CWempe/SuperLEDstrip/src/nextion_callback_functions.h

// Nextion components functions
// global
// page 1
void titlePopCallback(void *ptr) { }
void versionPopCallback(void *ptr) { }
void tempPopCallback(void *ptr) { }
void humidPopCallback(void *ptr) { }
void p01PopCallback(void *ptr) { }
void p01titlePopCallback(void *ptr) { }
void p01versionPopCallback(void *ptr) { }
void p01settingsPopCallback(void *ptr) { setTextAll(); }
void p01powerPopCallback(void *ptr) { toggleBrightness(); }
void p01t01PopCallback(void *ptr) { updateTab(); }
void p01t02PopCallback(void *ptr) { updateTab(); }
void p01t03PopCallback(void *ptr) { updateTab(); }
void p01t04PopCallback(void *ptr) { updateTab(); }
void p01t05PopCallback(void *ptr) { updateTab(); }
void p01t06PopCallback(void *ptr) { updateTab(); }
void p01t07PopCallback(void *ptr) { updateTab(); }
void p01c01PopCallback(void *ptr) { setScene(101); }
void p01c02PopCallback(void *ptr) { setScene(102); }
void p01c03PopCallback(void *ptr) { setScene(103); }
void p01c04PopCallback(void *ptr) { setScene(104); }
void p01c05PopCallback(void *ptr) { setScene(105); }
void p01c06PopCallback(void *ptr) { setScene(106); }
void p01c07PopCallback(void *ptr) { setScene(107); }
void p01c08PopCallback(void *ptr) { setScene(108); }
void p01c09PopCallback(void *ptr) { setScene(109); }
// page 2
void p02PopCallback(void *ptr) { }
void p02titlePopCallback(void *ptr) { }
void p02versionPopCallback(void *ptr) { }
void p02settingsPopCallback(void *ptr) { setTextAll(); }
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
void p06t04PopCallback(void *ptr) { updateTab(); }
void p06t05PopCallback(void *ptr) { updateTab(); }
void p06t06PopCallback(void *ptr) { updateTab(); }
void p06t07PopCallback(void *ptr) { updateTab(); }
void p06c01PopCallback(void *ptr) { setScene(601); }
void p06c02PopCallback(void *ptr) { setScene(602); }
void p06c03PopCallback(void *ptr) { setScene(603); }
void p06c04PopCallback(void *ptr) { }
void p06c05PopCallback(void *ptr) { }
void p06c06PopCallback(void *ptr) { }
void p06c07PopCallback(void *ptr) { }
void p06c08PopCallback(void *ptr) { }
// page 7
void p07PopCallback(void *ptr) { }
void p07titlePopCallback(void *ptr) { }
void p07versionPopCallback(void *ptr) { }
void p07settingsPopCallback(void *ptr) { setTextAll(); }
void p07powerPopCallback(void *ptr) { toggleBrightness(); }
void p07t01PopCallback(void *ptr) { updateTab(); }
void p07t02PopCallback(void *ptr) { updateTab(); }
void p07t03PopCallback(void *ptr) { updateTab(); }
void p07t04PopCallback(void *ptr) { updateTab(); }
void p07t05PopCallback(void *ptr) { updateTab(); }
void p07t06PopCallback(void *ptr) { updateTab(); }
void p07t07PopCallback(void *ptr) { updateTab(); }
void p07c01PopCallback(void *ptr) { setScene(110); }
void p07c02PopCallback(void *ptr) { setScene(112); }
void p07c03PopCallback(void *ptr) { setScene(111); }
void p07c04PopCallback(void *ptr) { }
void p07c05PopCallback(void *ptr) { setPalette(5); }
void p07c06PopCallback(void *ptr) { setPalette(3); }
void p07c07PopCallback(void *ptr) { setPalette(4); }
void p07c08PopCallback(void *ptr) { setPalette(100); }
void p07c09PopCallback(void *ptr) { setPalette(7); }
void p07c10PopCallback(void *ptr) { setPalette(102); }
void p07c11PopCallback(void *ptr) { }
void p07c12PopCallback(void *ptr) { }
void p07c13PopCallback(void *ptr) { }
void p07c14PopCallback(void *ptr) { }
void p07c15PopCallback(void *ptr) { }
void p07c16PopCallback(void *ptr) { }
// page 8
void p08PopCallback(void *ptr) { }
void p08titlePopCallback(void *ptr) { }
void p08versionPopCallback(void *ptr) { }
void p08settingsPopCallback(void *ptr) { setTextAll(); }
void p08powerPopCallback(void *ptr) { toggleBrightness(); }
void p08t01PopCallback(void *ptr) { updateTab(); }
void p08t02PopCallback(void *ptr) { updateTab(); }
void p08t03PopCallback(void *ptr) { updateTab(); }
void p08t04PopCallback(void *ptr) { updateTab(); }
void p08t05PopCallback(void *ptr) { updateTab(); }
void p08t06PopCallback(void *ptr) { updateTab(); }
void p08t07PopCallback(void *ptr) { updateTab(); }
void p08c01PopCallback(void *ptr) { setBrightness(DEFAULT_BRIGHTNESS); }
void p08c02PopCallback(void *ptr) { setBrightness(100); }
void p08c03PopCallback(void *ptr) { setBrightness(75); }
void p08c04PopCallback(void *ptr) { setBrightness(25); }
void p08c05PopCallback(void *ptr) { setTextTemp(); }
void p08c06PopCallback(void *ptr) { setTextHumid(); }
void p08c07PopCallback(void *ptr) { changeRotationSpeed(true); }
void p08c08PopCallback(void *ptr) { changeRotationSpeed(false); }
void p08temp02PopCallback(void *ptr) { }
void p08humid02PopCallback(void *ptr) { }
void p08speed01PopCallback(void *ptr) { changeRotationSpeed(true); }
// page 9
void p09PopCallback(void *ptr) { }
void p09titlePopCallback(void *ptr) { }
void p09versionPopCallback(void *ptr) { }
void p09settingsPopCallback(void *ptr) { setTextAll(); }
void p09powerPopCallback(void *ptr) { toggleBrightness(); }
void p09sliderRedPopCallback(void *ptr)    { getRed(); }
void p09redMPopCallback(void *ptr)         { getRed(); }
void p09redPPopCallback(void *ptr)         { getRed(); }
void p09sliderGreenPopCallback(void *ptr)  { getGreen(); }
void p09greenMPopCallback(void *ptr)       { getGreen(); }
void p09greenPPopCallback(void *ptr)       { getGreen(); }
void p09sliderBluePopCallback(void *ptr)   { getBlue(); }
void p09blueMPopCallback(void *ptr)        { getBlue(); }
void p09bluePPopCallback(void *ptr)        { getBlue(); }
void p09save1PopCallback(void *ptr)        { saveCustomColorPreset (1); }
void p09load1PopCallback(void *ptr)        { loadCustomColorPreset (1); }
void p09save2PopCallback(void *ptr)        { saveCustomColorPreset (2);  }
void p09load2PopCallback(void *ptr)        { loadCustomColorPreset (2);  }
