CWempe/SuperLEDstrip/src/nextion_declaration.h

// Nextion components deklaration
// global
// page 1


char sRotationSpeed[2] = "";

NexText   title       = NexText(  0, 19, "title");
NexText   version     = NexText(  0, 24, "version");
NexText   temp        = NexText(  0, 20, "temp");
NexText   humid       = NexText(  0, 21, "humid");

NexPage   p01         = NexPage(  0,  0, "p01");
NexText   p01title    = NexText(  0,  1, "p01title");
NexText   p01version  = NexText(  0, 25, "p01version");
NexButton p01settings = NexButton(0,  9, "p01settings");
NexButton p01power    = NexButton(0, 18, "p01power");
NexButton p01t01      = NexButton(0,  2, "p01t01");
NexButton p01t02      = NexButton(0,  3, "p01t02");
NexButton p01t03      = NexButton(0,  4, "p01t03");
NexButton p01t04      = NexButton(0,  5, "p01t04");
NexButton p01t05      = NexButton(0,  6, "p01t05");
NexButton p01t06      = NexButton(0,  7, "p01t06");
NexButton p01t07      = NexButton(0,  8, "p01t07");
NexButton p01c01      = NexButton(0, 10, "p01c01");
NexButton p01c02      = NexButton(0, 11, "p01c02");
NexButton p01c03      = NexButton(0, 12, "p01c03");
NexButton p01c04      = NexButton(0, 13, "p01c04");
NexButton p01c05      = NexButton(0, 14, "p01c05");
NexButton p01c06      = NexButton(0, 15, "p01c06");
NexButton p01c07      = NexButton(0, 16, "p01c07");
NexButton p01c08      = NexButton(0, 17, "p01c08");
NexButton p01c09      = NexButton(0, 23, "p01c09");
// page 2
NexPage   p02         = NexPage(  1,  0, "p02");
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
NexButton p08t04      = NexButton(7,  5, "p08t04");
NexButton p08t05      = NexButton(7,  6, "p08t05");
NexButton p08t06      = NexButton(7,  7, "p08t06");
NexButton p08t07      = NexButton(7,  8, "p08t07");
NexButton p08c01      = NexButton(7, 10, "p08c01");
NexButton p08c02      = NexButton(7, 11, "p08c02");
NexButton p08c03      = NexButton(7, 12, "p08c03");
NexButton p08c04      = NexButton(7, 13, "p08c04");
NexButton p08c05      = NexButton(7, 14, "p08c05");
NexButton p08c06      = NexButton(7, 15, "p08c06");
NexButton p08c07      = NexButton(7, 16, "p08c07");
NexButton p08c08      = NexButton(7, 17, "p08c08");
NexText   p08temp02   = NexText(  7, 19, "p08temp02");
NexText   p08humid02  = NexText(  7, 20, "p08humid02");
NexText   p08speed01  = NexText(  7, 29, "p08speed01");

// page 9
NexPage   p09            = NexPage(  8,  0, "p09");
NexText   p09title       = NexText(  8,  1, "p09title");
NexText   p09version     = NexText(  8, 31, "p09version");
NexButton p09settings    = NexButton(8, 10, "p09settings");
NexButton p09power       = NexButton(8, 12, "p09power");
NexSlider p09sliderRed   = NexSlider(8, 14, "p09sliderRed");
NexSlider p09sliderGreen = NexSlider(8, 15, "p09sliderGreen");
NexSlider p09sliderBlue  = NexSlider(8, 26, "p09sliderBlue");
NexButton p09redM        = NexButton(8, 11, "p09redM");
NexButton p09redP        = NexButton(8, 19, "p09redP");
NexButton p09greenM      = NexButton(8, 21, "p09greenM");
NexButton p09greenP      = NexButton(8, 22, "p09greenP");
NexButton p09blueM       = NexButton(8, 24, "p09blueM");
NexButton p09blueP       = NexButton(8, 25, "p09blueP");
NexText   p09red         = NexText(  8, 13, "p09red");
NexText   p09green       = NexText(  8, 20, "p09green");
NexText   p09blue        = NexText(  8, 23, "p09blue");
NexButton p09save1       = NexButton(8, 27, "p09save1");
NexButton p09load1       = NexButton(8, 29, "p09load1");
NexButton p09save2       = NexButton(8, 28, "p09save2");
NexButton p09load2       = NexButton(8, 30, "p09load2");
