CWempe/SuperLEDstrip/src/nextion_initialization.h

// Nextion components inizialization
// global
void NextionSetup()
{
    nexInit();
    // page 1
    p01.attachPop(p01PopCallback);
    title.attachPop(titlePopCallback);
    version.attachPop(versionPopCallback);
    p01title.attachPop(p01titlePopCallback);
    p01version.attachPop(p01versionPopCallback);
    p01settings.attachPop(p01settingsPopCallback);
    p01power.attachPop(p01powerPopCallback);
    p01t01.attachPop(p01t01PopCallback);
    p01t02.attachPop(p01t02PopCallback);
    p01t03.attachPop(p01t03PopCallback);
    p01t04.attachPop(p01t04PopCallback);
    p01t05.attachPop(p01t05PopCallback);
    p01t06.attachPop(p01t06PopCallback);
    p01t07.attachPop(p01t07PopCallback);
    p01c01.attachPop(p01c01PopCallback);
    p01c02.attachPop(p01c02PopCallback);
    p01c03.attachPop(p01c03PopCallback);
    p01c04.attachPop(p01c04PopCallback);
    p01c05.attachPop(p01c05PopCallback);
    p01c06.attachPop(p01c06PopCallback);
    p01c07.attachPop(p01c07PopCallback);
    p01c08.attachPop(p01c08PopCallback);
    p01c09.attachPop(p01c09PopCallback);
    // page 2
    p02.attachPop(p02PopCallback);
    p02title.attachPop(p02titlePopCallback);
    p02version.attachPop(p02versionPopCallback);
    p02settings.attachPop(p02settingsPopCallback);
    p02power.attachPop(p02powerPopCallback);
    p02t01.attachPop(p02t01PopCallback);
    p02t02.attachPop(p02t02PopCallback);
    p02t03.attachPop(p02t03PopCallback);
    p02t04.attachPop(p02t04PopCallback);
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
    p07t02.attachPop(p07t02PopCallback);
    p07t03.attachPop(p07t03PopCallback);
    p07t04.attachPop(p07t04PopCallback);
    p07t05.attachPop(p07t05PopCallback);
    p07t06.attachPop(p07t06PopCallback);
    p07t07.attachPop(p07t07PopCallback);
    p07c01.attachPop(p07c01PopCallback);
    p07c02.attachPop(p07c02PopCallback);
    p07c03.attachPop(p07c03PopCallback);
    p07c04.attachPop(p07c04PopCallback);
    p07c05.attachPop(p07c05PopCallback);
    p07c06.attachPop(p07c06PopCallback);
    p07c07.attachPop(p07c07PopCallback);
    p07c08.attachPop(p07c08PopCallback);
    p07c09.attachPop(p07c09PopCallback);
    p07c10.attachPop(p07c10PopCallback);
    p07c11.attachPop(p07c11PopCallback);
    p07c12.attachPop(p07c12PopCallback);
    p07c13.attachPop(p07c13PopCallback);
    p07c14.attachPop(p07c14PopCallback);
    p07c15.attachPop(p07c15PopCallback);
    p07c16.attachPop(p07c16PopCallback);
    // page 8
    p08.attachPop(p08PopCallback);
    p08title.attachPop(p08titlePopCallback);
    p08version.attachPop(p08versionPopCallback);
    p08settings.attachPop(p08settingsPopCallback);
    p08power.attachPop(p08powerPopCallback);
    p08t01.attachPop(p08t01PopCallback);
    p08t02.attachPop(p08t02PopCallback);
    p08t03.attachPop(p08t03PopCallback);
    p08t04.attachPop(p08t04PopCallback);
    p08t05.attachPop(p08t05PopCallback);
    p08t06.attachPop(p08t06PopCallback);
    p08t07.attachPop(p08t07PopCallback);
    p08c01.attachPop(p08c01PopCallback);
    p08c02.attachPop(p08c02PopCallback);
    p08c03.attachPop(p08c03PopCallback);
    p08c04.attachPop(p08c04PopCallback);
    p08c05.attachPop(p08c05PopCallback);
    p08c06.attachPop(p08c06PopCallback);
    p08c07.attachPop(p08c07PopCallback);
    p08c08.attachPop(p08c08PopCallback);
    p08temp02.attachPop(p08temp02PopCallback);
    p08humid02.attachPop(p08humid02PopCallback);
    p08speed01.attachPop(p08speed01PopCallback);
    // page 9
    p09.attachPop(p09PopCallback);
    p09title.attachPop(p09titlePopCallback);
    p09version.attachPop(p09versionPopCallback);
    p09settings.attachPop(p09settingsPopCallback);
    p09power.attachPop(p09powerPopCallback);
    p09sliderRed.attachPop(p09sliderRedPopCallback);
    p09redM.attachPop(p09redMPopCallback);
    p09redP.attachPop(p09redPPopCallback);
    p09sliderGreen.attachPop(p09sliderGreenPopCallback);
    p09greenM.attachPop(p09greenMPopCallback);
    p09greenP.attachPop(p09greenPPopCallback);
    p09sliderBlue.attachPop(p09sliderBluePopCallback);
    p09blueM.attachPop(p09blueMPopCallback);
    p09blueP.attachPop(p09bluePPopCallback);
    p09save1.attachPop(p09save1PopCallback);
    p09save2.attachPop(p09save2PopCallback);
    p09load1.attachPop(p09load1PopCallback);
    p09load2.attachPop(p09load2PopCallback);
    //
    dbSerialPrintln("setup done");
}
