CWempe/SuperLEDstrip/src/nextion_functions.h

void setTextTitle()
{
  char cVersion[10] = "v";
  strcat(cVersion, HOMIE_FW_VERSION);
  title.setText(DISPLAY_TITLE);
  version.setText(cVersion);
  p01title.setText(DISPLAY_TITLE);
  p01version.setText(cVersion);
}

void setTextTemp()
{
  #if defined(SENSOR_DS18B20) || defined(SENSOR_DHT)
    temp.setText(sTemp);
    p08temp02.setText(sTemp);
  #endif
}

void setTextHumid()
{
  #ifdef SENSOR_DHT
    humid.setText(sHumid);
    p08humid02.setText(sHumid);
  #endif
}

void setTextAllSensors()
{
  #if defined(SENSOR_DS18B20) || defined(SENSOR_DHT)
    setTextTemp();
  #endif
  #ifdef SENSOR_DHT
    setTextHumid();
  #endif
}

void setTextRotationSpeed()
{
    dtostrf(rotationSpeed, 3, 0, sRotationSpeed);
    p08speed01.setText(sRotationSpeed);
}

void setTextAll()
{
    setTextTitle();
    setTextAllSensors();
    setTextRotationSpeed();
}

void updateTab()
{
  setTextAll();
}

void updateRotationSpeed () {
  if (Homie.isConnected()) lightNode.setProperty("rotationSpeed").send(String(rotationSpeed));
  rotationSpeedMs = 3 * rotationSpeed * rotationSpeed - 120 * rotationSpeed + 1200;
  if ( rotationSpeedMs < 1 ) {
    rotationSpeedMs = 1;
  }
  ColorRotation.setPeriod(rotationSpeedMs);
  // Deactivated setTextRotationSpeed() here because it can produce "wdt reset"
  //setTextRotationSpeed();
  // store current scene number to eeprom
  Embedis::set("rotationSpeedValue", String(rotationSpeed));
}

void changeRotationSpeed (bool increaseSpeed)
{
  if ( increaseSpeed == true && rotationSpeed < 20 ) {
     rotationSpeed++;
  } else if ( increaseSpeed == false && rotationSpeed > 1 ) {
    rotationSpeed--;
  }
  // setTextRotationSpeed() can be deleted here if bug from updateRotationSpeed() is fixed
  setTextRotationSpeed();
  updateRotationSpeed();
}

void getRed ()
{
  uint32_t red = 999;
  p09sliderRed.getValue(&red);
  Homie.getLogger() << "Red: " << red << endl;
  // Sometimes getValue does not get the value so we try again
  if ( red != 999) {
    p09sliderRed.getValue(&red);
    Homie.getLogger() << "Red: " << red << endl;
  }
  if ( red != 999) {
    updateCustomColorRed(red);
  }  
}

void getGreen ()
{
  uint32_t green = 999;
  p09sliderGreen.getValue(&green);
  Homie.getLogger() << "Green: " << green << endl;
  // Sometimes getValue does not get the value so we try again
  if ( green != 999) {
    p09sliderGreen.getValue(&green);
    Homie.getLogger() << "Green: " << green << endl;
  }
  if ( green != 999) {
    updateCustomColorGreen(green);
  }
}


void getBlue ()
{
  uint32_t blue = 999;
  p09sliderBlue.getValue(&blue);
  Homie.getLogger() << "Blue: " << blue << endl;
  // Sometimes getValue does not get the value so we try again
  if ( blue != 999) {
    p09sliderBlue.getValue(&blue);
    Homie.getLogger() << "Blue: " << blue << endl;
  }
  if ( blue != 999) {
    updateCustomColorBlue(blue);
  }
}

void setRed ()
{
    uint8_t red = customColor.red;

    // set slider
    delay (10);     // a short delay to make the setValue work more stable
    p09sliderRed.setValue(red);
    delay (10);
    
    // set value next to slider; needs to be converted to char
    char sRed[4];
    dtostrf(red, 3, 0, sRed);
    p09red.setText(sRed);

    updateDisplayRed = false;
}

void setGreen ()
{
    uint8_t green = customColor.green;

    // set slider
    delay (10);     // a short delay to make the setValue work more stable
    p09sliderGreen.setValue(green);
    delay (10);
    
    // set value next to slider; needs to be converted to char
    char sGreen[4];
    dtostrf(green, 3, 0, sGreen);
    p09green.setText(sGreen);

    updateDisplayGreen = false;
}

void setBlue ()
{
    uint8_t blue = customColor.blue;

    // set slider
    delay (10);     // a short delay to make the setValue work more stable
    p09sliderBlue.setValue(blue);
    delay (10);
    
    // set value next to slider; needs to be converted to char
    char sBlue[4];
    dtostrf(blue, 3, 0, sBlue);
    p09blue.setText(sBlue);

    updateDisplayBlue= false;
}

// this function is used because directly `setValue` in updateCustomColor* causes the program to crash
void updateDisplayColors ()
{
    if ( updateDisplayRed   == true ) { setRed();   delay(10);}
    if ( updateDisplayGreen == true ) { setGreen(); delay(10);}
    if ( updateDisplayBlue  == true ) { setBlue(); }
}
