CWempe/SuperLEDstrip/src/global_values.h

/*
 * This file contains global variables .
 * Variables can be overritten by custom_values.h
 */

/*
 * Homie parameters
 */
#define HOMIE_FW_NAME     "SuperLEDstrip"
#define HOMIE_FW_VERSION  "3.1.0"
